VinFar/ESP32-Lichtwecker/ESP32-Lichtwecker/include/WebServerAlarmTab.h

#ifndef WEBSERVERALARMTAB_H_
#define WEBSERVERALARMTAB_H_

#include <ESPUI.h>
#include "AlarmTask.h"

void slider(Control *sender, int type);
void WebUiAlarmTabInit();
void WebUiAlarmSwitchSetState(const uint16_t Id, const bool newState);
void WebUiAlarmSwitchUpdateAll();
int8_t WebUiAlarmGetIndexById(uint16_t id);
void WebUiAlarmTabCreate();

#endif
