VinFar/ESP32-Lichtwecker/ESP32-Lichtwecker/include/WebServerStatusTab.h

#ifndef WEBSERVERSTATUS_H_
#define WEBSERVERSTATUS_H_

void WebUiStatusTabInit();
uint16_t WebUiGetTemperatureLabelId();
void WebUiLedPwmUpdateLabel(float DutyCycle);
void WebUiStatusTabCreate();

#endif
